Miramaksimus/HOTAS-Joystick-Soleil/images/3.png

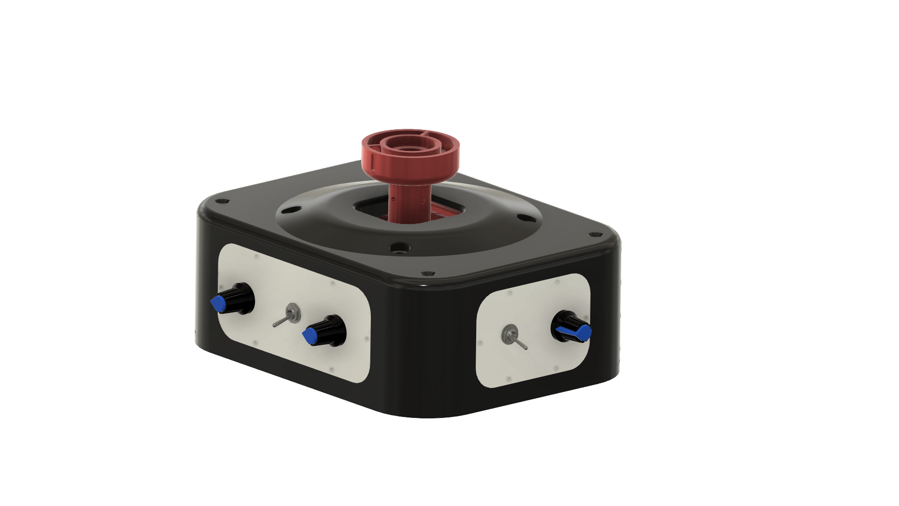
images/3.png
