Miramaksimus/HOTAS-Joystick-Soleil/export/housing/rectangular/stl/box_frame.stl

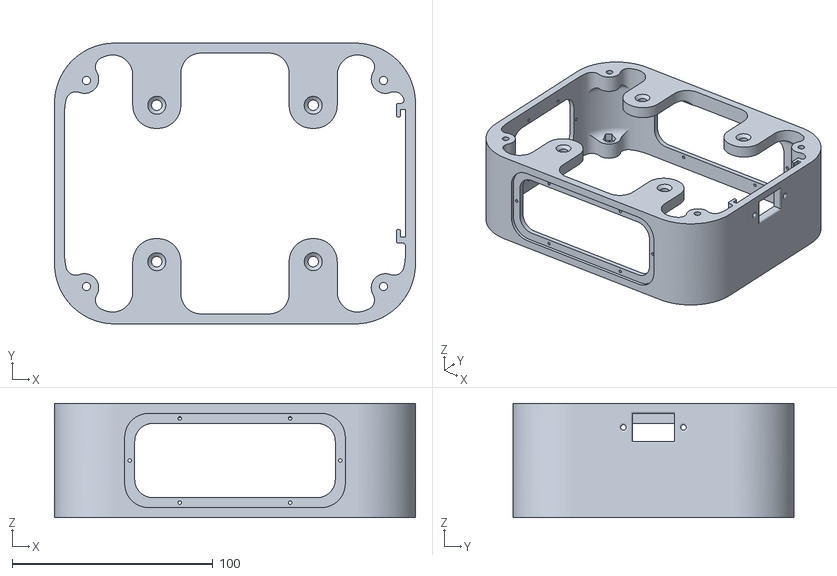
[picture p22: CAD file, 2023-05-21]
export/housing/rectangular/stl/box_frame.stl
180.0 x 140.0 x 57.0
