Miramaksimus/HOTAS-Joystick-Soleil/export/stick/common_parts/stl/dms_hat.stl

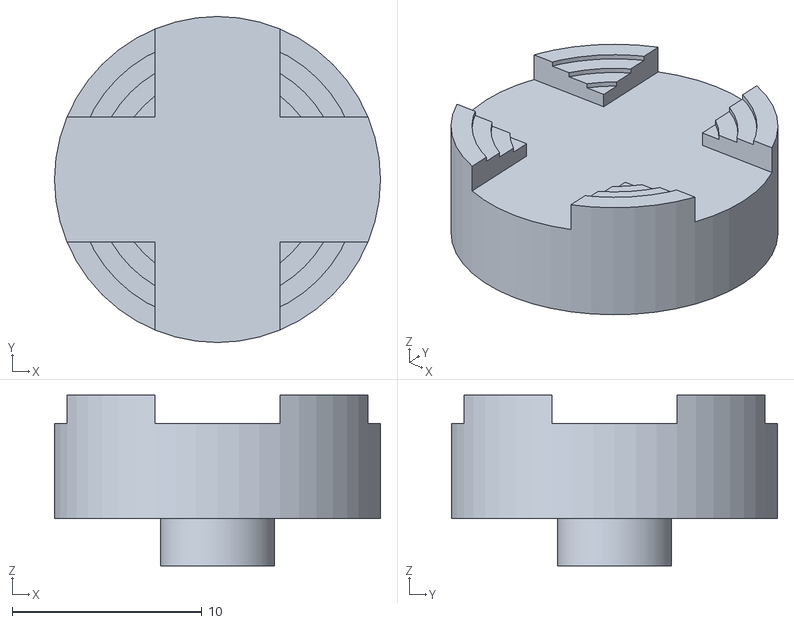
[picture p23: CAD file, 2024-08-11]
export/stick/common_parts/stl/dms_hat.stl
17.2 x 17.2 x 9.00
