Miramaksimus/HOTAS-Joystick-Soleil/export/twist/stl/gimbal_lever_arm.stl

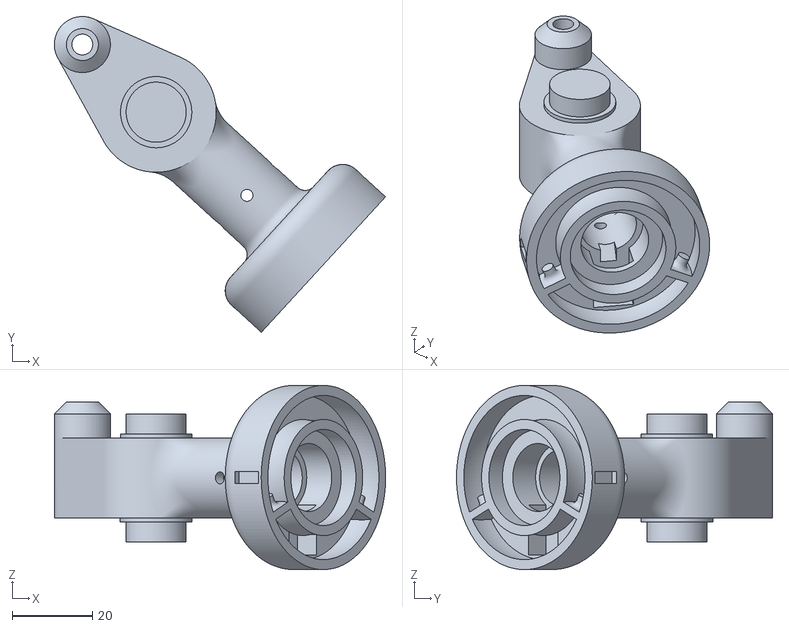
[picture p24: CAD file, 2023-04-30]
export/twist/stl/gimbal_lever_arm.stl
82.7 x 78.9 x 46.0
