Miramaksimus/HOTAS-Joystick-Soleil/export/gimbal/stl/gimbal_core_bearing_carrier_alt.stl

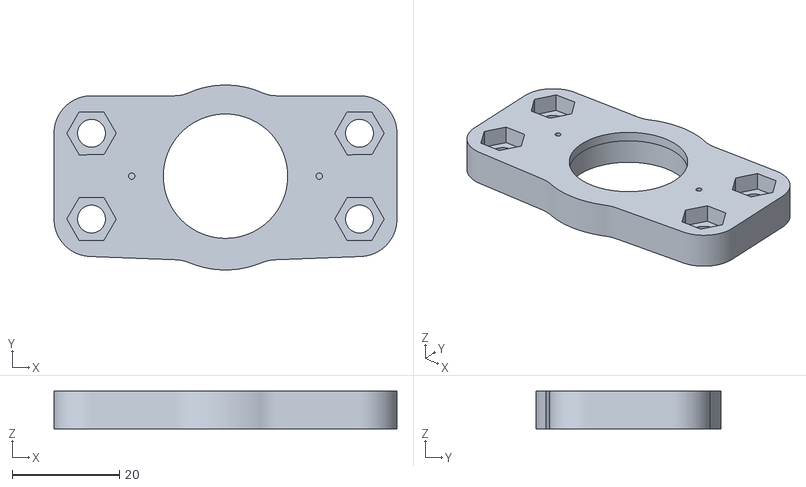
[picture p25: CAD file, 2023-04-30]
export/gimbal/stl/gimbal_core_bearing_carrier_alt.stl
64.0 x 34.5 x 7.00
