Miramaksimus/HOTAS-Joystick-Soleil/export/housing/cylindrical/stl/housing_body.stl

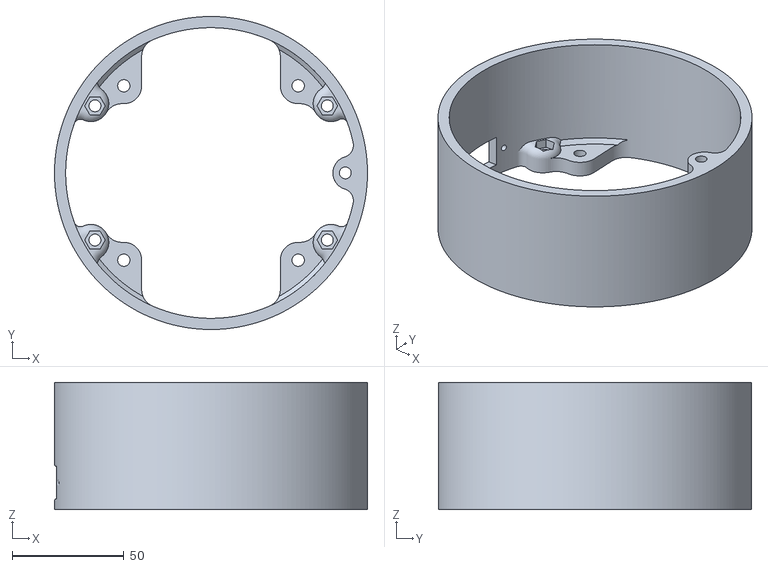
[picture p26: CAD file, 2023-04-30]
export/housing/cylindrical/stl/housing_body.stl
140.0 x 140.0 x 57.0
