Miramaksimus/HOTAS-Joystick-Soleil/export/housing/rectangular/stl/front_cover.stl

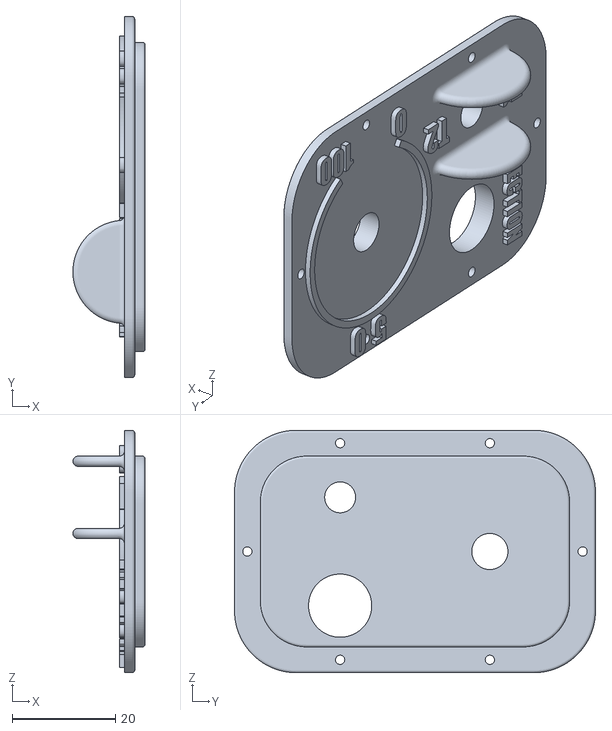
[picture p27: CAD file, 2023-05-21]
export/housing/rectangular/stl/front_cover.stl
14.0 x 70.0 x 47.0
