Miramaksimus/HOTAS-Joystick-Soleil/export/stick/common_parts/stl/tact_switch_cover.stl

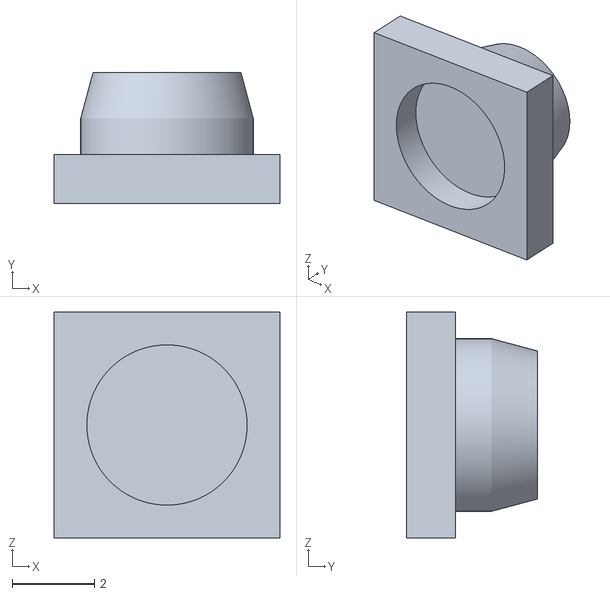
[picture p28: CAD file, 2024-08-11]
export/stick/common_parts/stl/tact_switch_cover.stl
5.50 x 3.20 x 5.50
