Miramaksimus/HOTAS-Joystick-Soleil/export/twist/stl/twist_adapder_top.stl

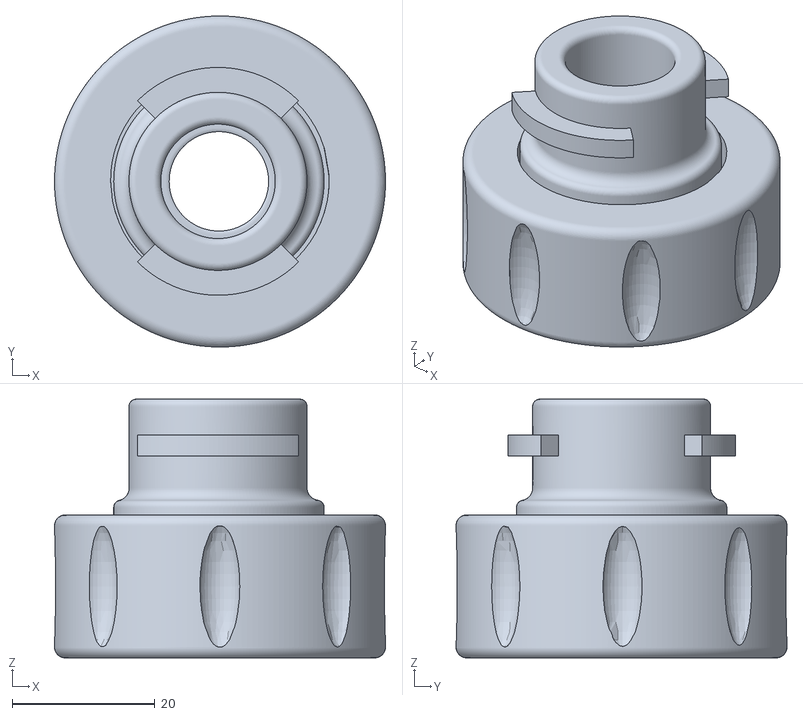
[picture p29: CAD file, 2023-04-30]
export/twist/stl/twist_adapder_top.stl
46.3 x 46.3 x 36.2
