Miramaksimus/HOTAS-Joystick-Soleil/export/gimbal/stl/gimbal_core_non_pot_side.stl

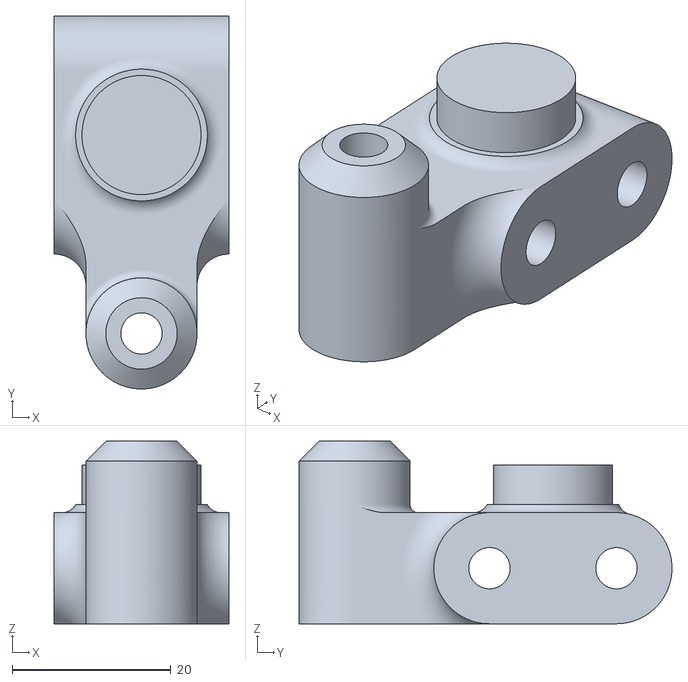
[picture p30: CAD file, 2023-04-30]
export/gimbal/stl/gimbal_core_non_pot_side.stl
22.0 x 47.0 x 23.0
