Miramaksimus/HOTAS-Joystick-Soleil/export/housing/cylindrical/stl/housing_bluepill-1.6mm.stl

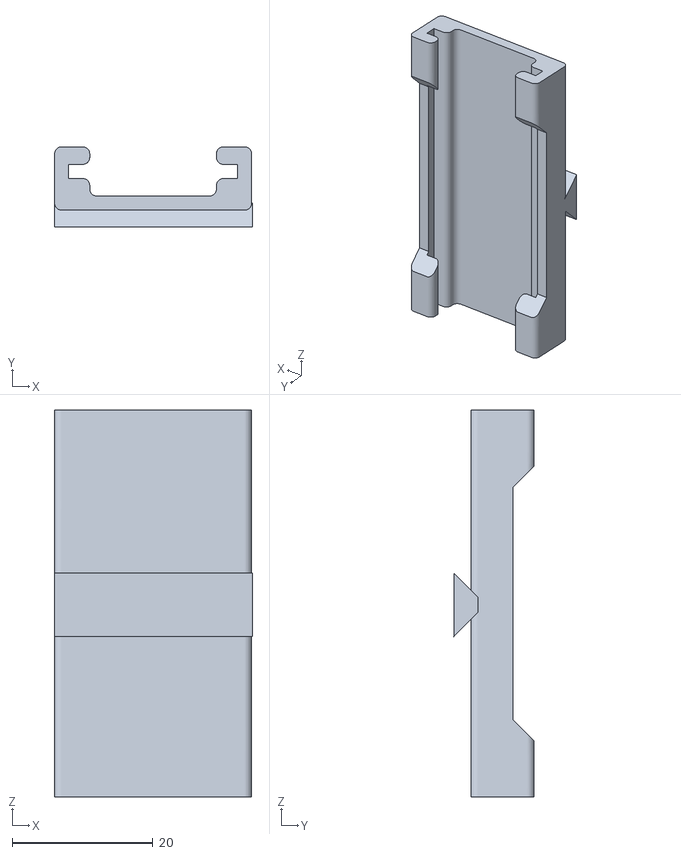
[picture p31: CAD file, 2023-04-30]
export/housing/cylindrical/stl/housing_bluepill-1.6mm.stl
28.2 x 11.4 x 55.0
