Miramaksimus/HOTAS-Joystick-Soleil/export/housing/rectangular/stl/box_bottom.stl

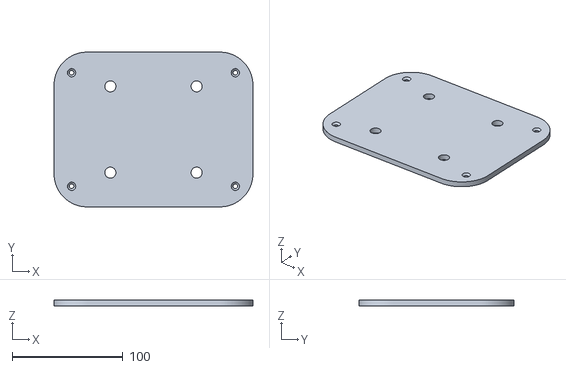
[picture p32: CAD file, 2023-05-21]
export/housing/rectangular/stl/box_bottom.stl
180.0 x 140.0 x 5.00
