Miramaksimus/HOTAS-Joystick-Soleil/export/stick/common_parts/stl/paddle.stl

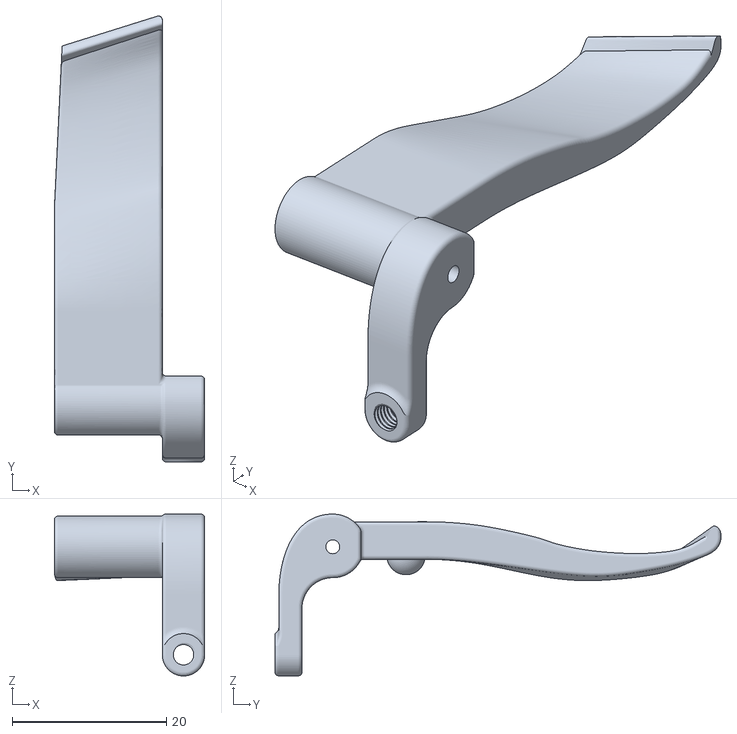
[picture p33: CAD file, 2024-08-11]
export/stick/common_parts/stl/paddle.stl
19.5 x 57.9 x 21.0
