Miramaksimus/HOTAS-Joystick-Soleil/export/twist/stl/twist_rudder_controls_top.stl

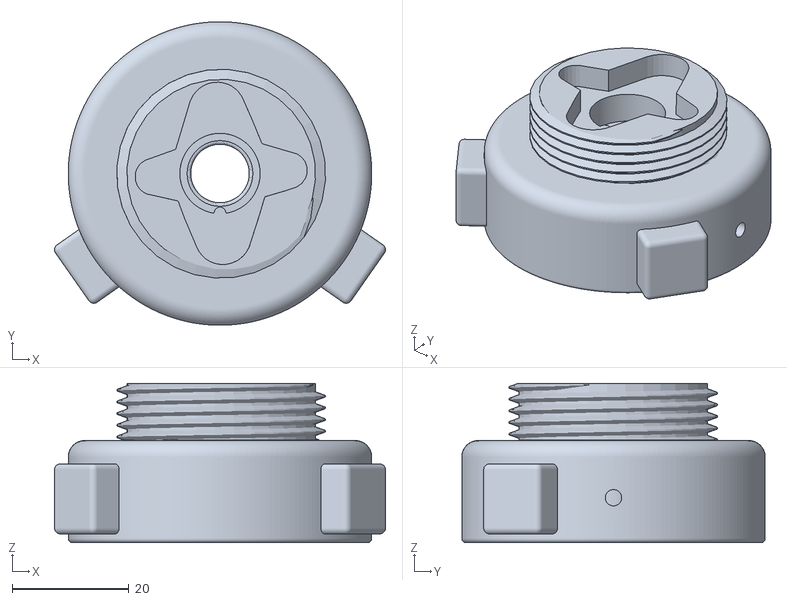
[picture p34: CAD file, 2023-04-30]
export/twist/stl/twist_rudder_controls_top.stl
56.7 x 52.0 x 27.3
