Miramaksimus/HOTAS-Joystick-Soleil/export/gimbal/stl/gimbal_cam.stl

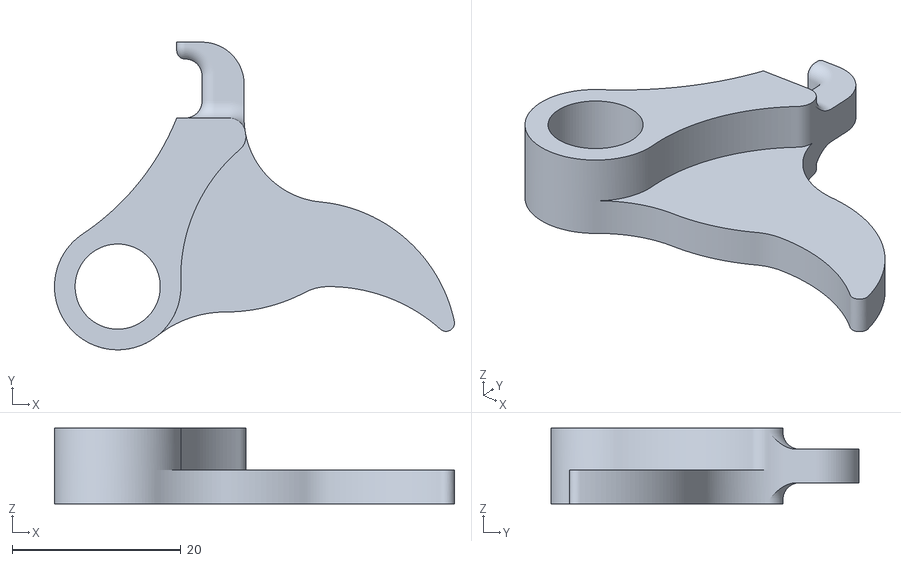
[picture p35: CAD file, 2023-04-30]
export/gimbal/stl/gimbal_cam.stl
47.5 x 36.5 x 9.00
