Miramaksimus/HOTAS-Joystick-Soleil/export/housing/rectangular/stl/right_cover.stl

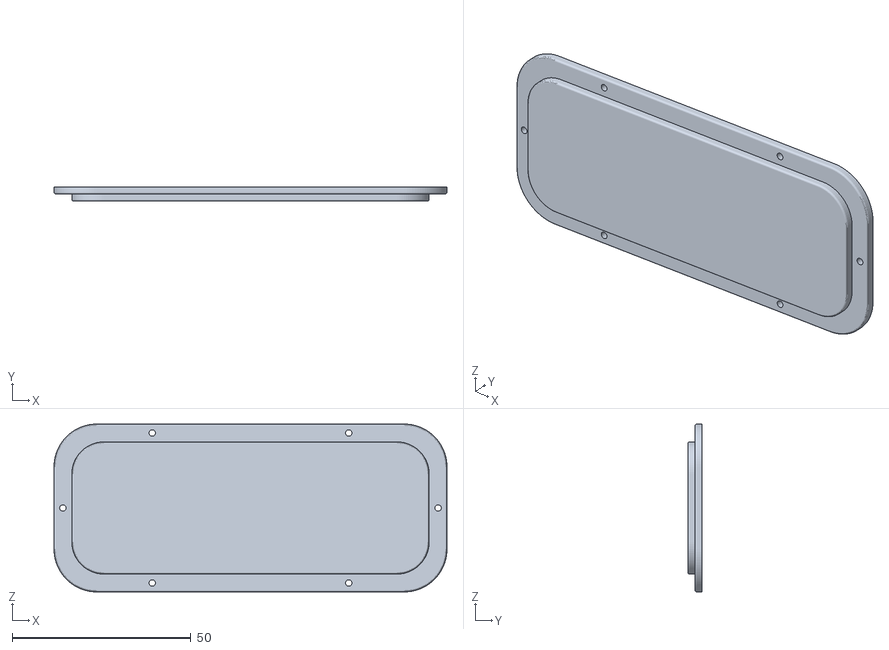
[picture p36: CAD file, 2023-05-21]
export/housing/rectangular/stl/right_cover.stl
110.0 x 4.00 x 47.0
