Miramaksimus/HOTAS-Joystick-Soleil/export/stick/common_parts/stl/trim_hat.stl

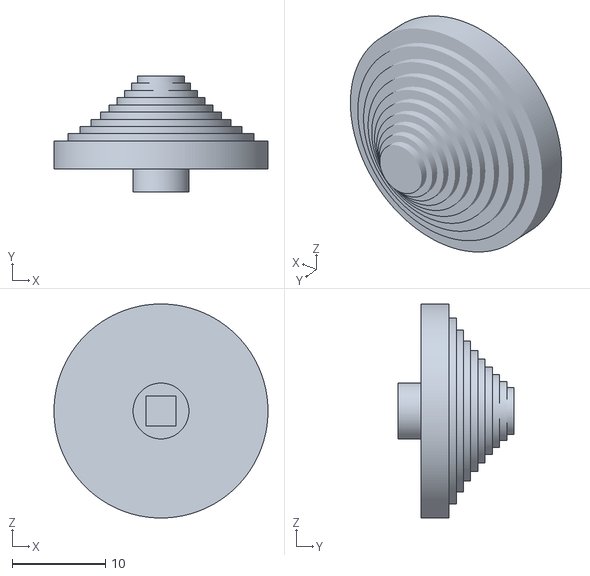
[picture p37: CAD file, 2024-08-11]
export/stick/common_parts/stl/trim_hat.stl
23.0 x 12.5 x 23.0
