Miramaksimus/HOTAS-Joystick-Soleil/export/housing/rectangular/stl/left_cover.stl

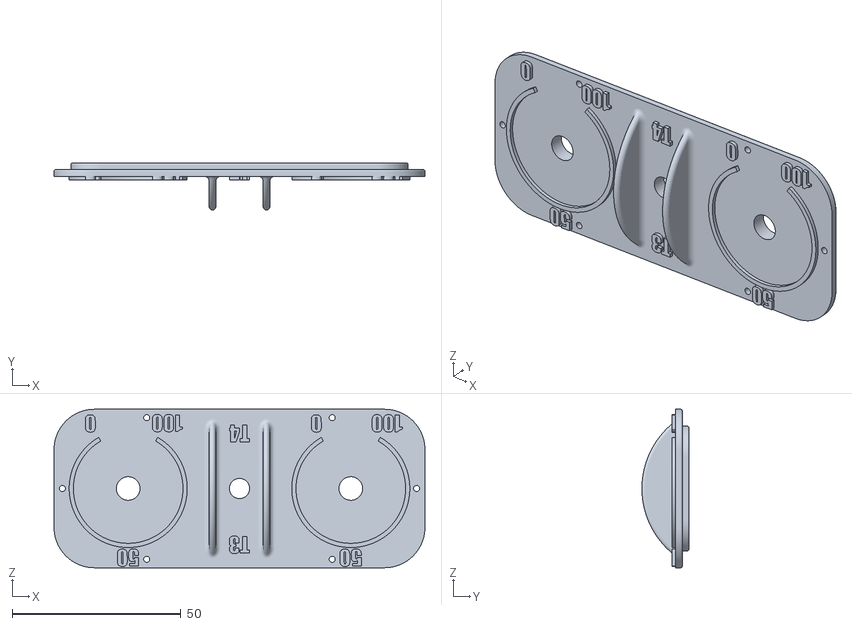
[picture p38: CAD file, 2023-05-21]
export/housing/rectangular/stl/left_cover.stl
110.0 x 14.0 x 47.0
