Miramaksimus/HOTAS-Joystick-Soleil/export/stick/common_parts/stl/tms_hat.stl

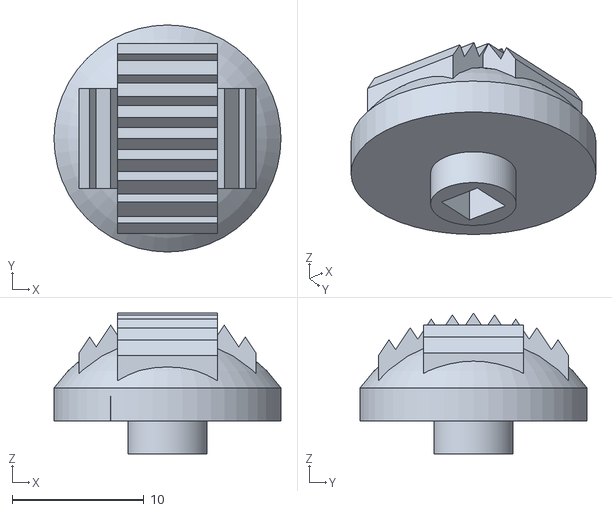
[picture p39: CAD file, 2024-08-11]
export/stick/common_parts/stl/tms_hat.stl
17.2 x 17.2 x 10.7
