Miramaksimus/HOTAS-Joystick-Soleil/export/housing/rectangular/stl/potentiometr_knob.stl

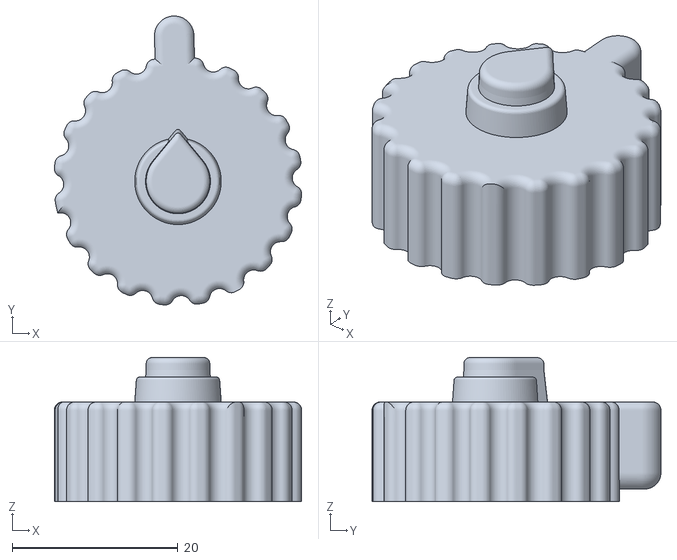
[picture p40: CAD file, 2023-05-21]
export/housing/rectangular/stl/potentiometr_knob.stl
29.8 x 34.8 x 17.4
