Miramaksimus/HOTAS-Joystick-Soleil/export/stick/common_parts/stl/button_side.stl

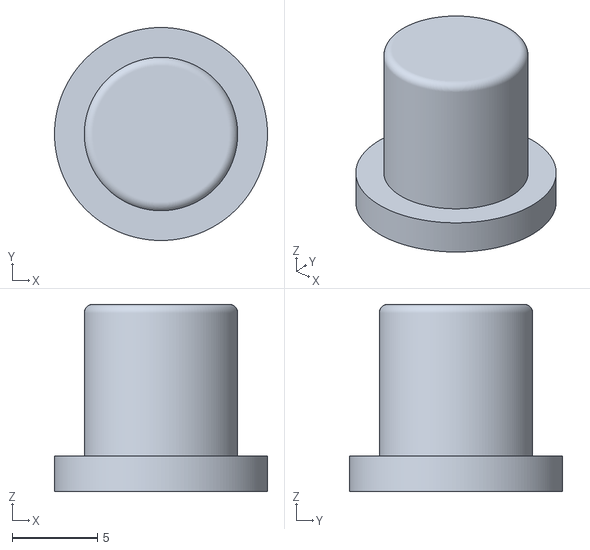
[picture p41: CAD file, 2024-08-11]
export/stick/common_parts/stl/button_side.stl
12.5 x 12.5 x 11.0
