Miramaksimus/HOTAS-Joystick-Soleil/export/housing/rectangular/stl/box_cover.stl

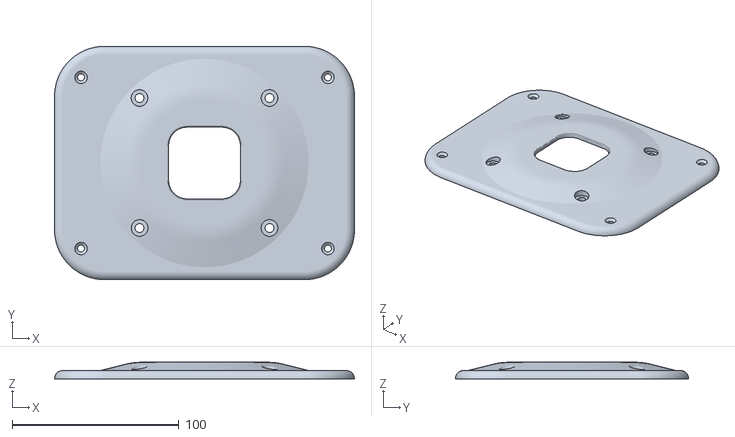
[picture p42: CAD file, 2023-05-21]
export/housing/rectangular/stl/box_cover.stl
180.0 x 140.0 x 10.0
