Miramaksimus/HOTAS-Joystick-Soleil/export/stick/common_parts/stl/trigger.stl

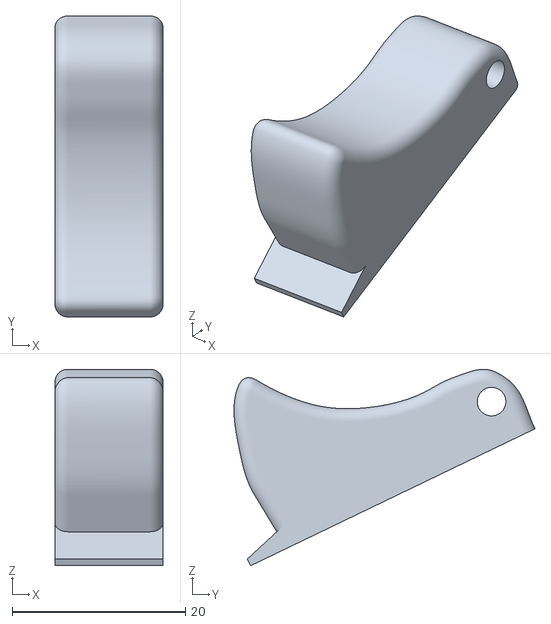
[picture p43: CAD file, 2024-08-11]
export/stick/common_parts/stl/trigger.stl
12.5 x 34.8 x 22.7
