Miramaksimus/HOTAS-Joystick-Soleil/export/housing/rectangular/stl/button_red_cap.stl

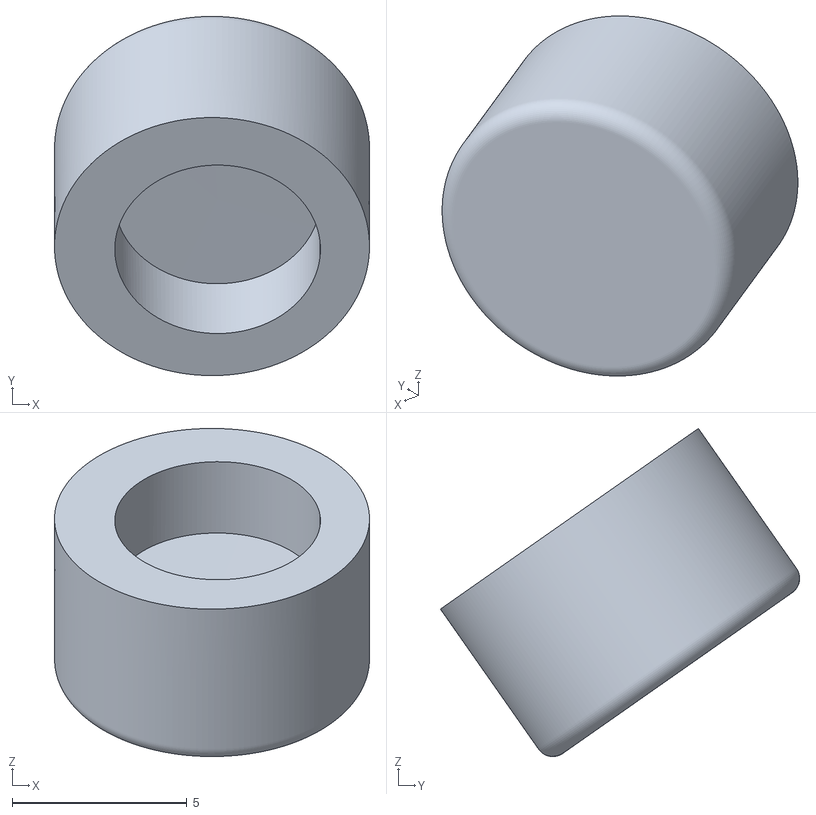
[picture p44: CAD file, 2023-05-21]
export/housing/rectangular/stl/button_red_cap.stl
9.00 x 10.3 x 9.37
