Miramaksimus/HOTAS-Joystick-Soleil/export/stick/common_parts/stl/button_ctrl.stl

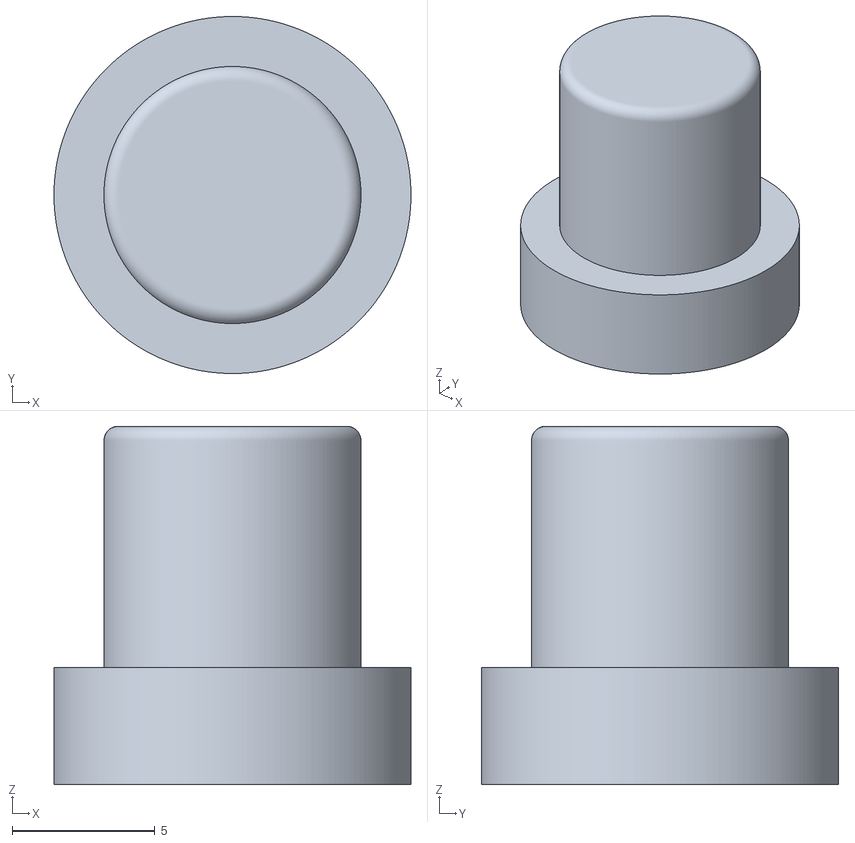
[picture p45: CAD file, 2024-08-11]
export/stick/common_parts/stl/button_ctrl.stl
12.5 x 12.5 x 12.5
