Miramaksimus/HOTAS-Joystick-Soleil/export/housing/rectangular/stl/soleil.stl

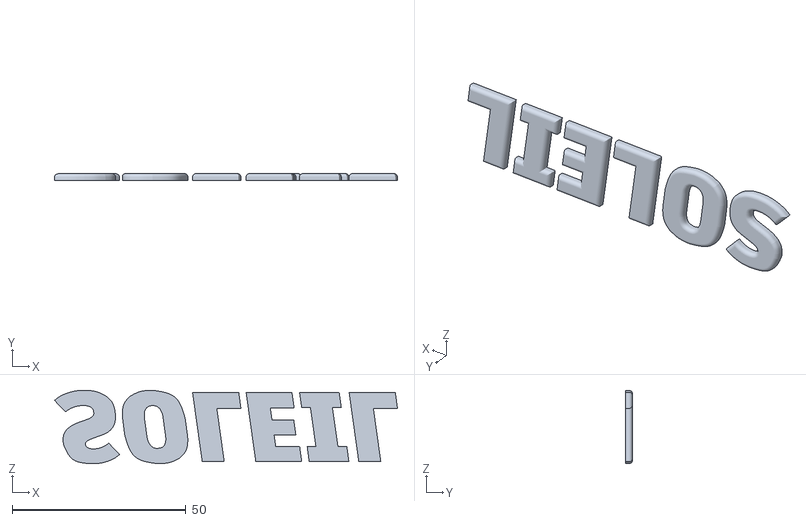
[picture p46: CAD file, 2023-05-21]
export/housing/rectangular/stl/soleil.stl
98.8 x 2.00 x 21.1
