Miramaksimus/HOTAS-Joystick-Soleil/export/stick/common_parts/stl/hat-switch-base.stl

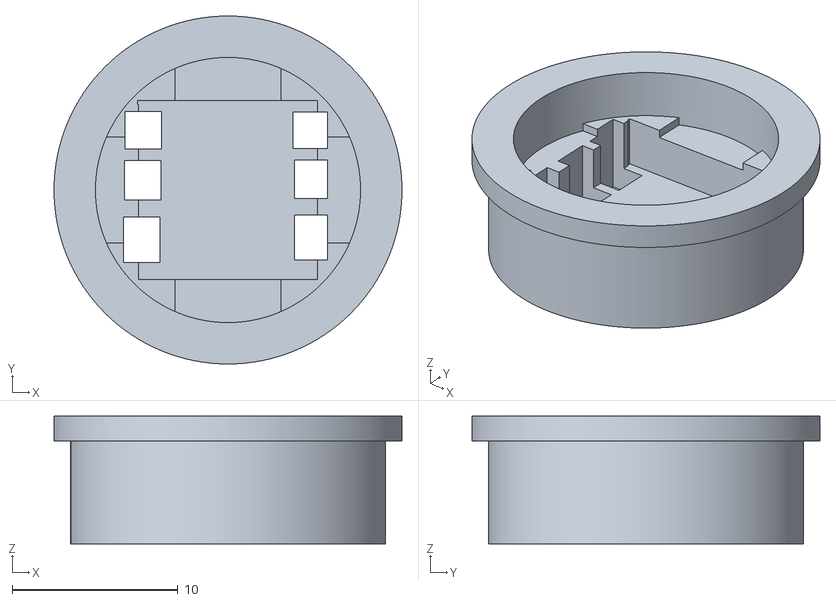
[picture p47: CAD file, 2023-06-24]
export/stick/common_parts/stl/hat-switch-base.stl
21.0 x 21.0 x 7.70
