Miramaksimus/HOTAS-Joystick-Soleil/export/stick/common_parts/stl/Face_alter.stl

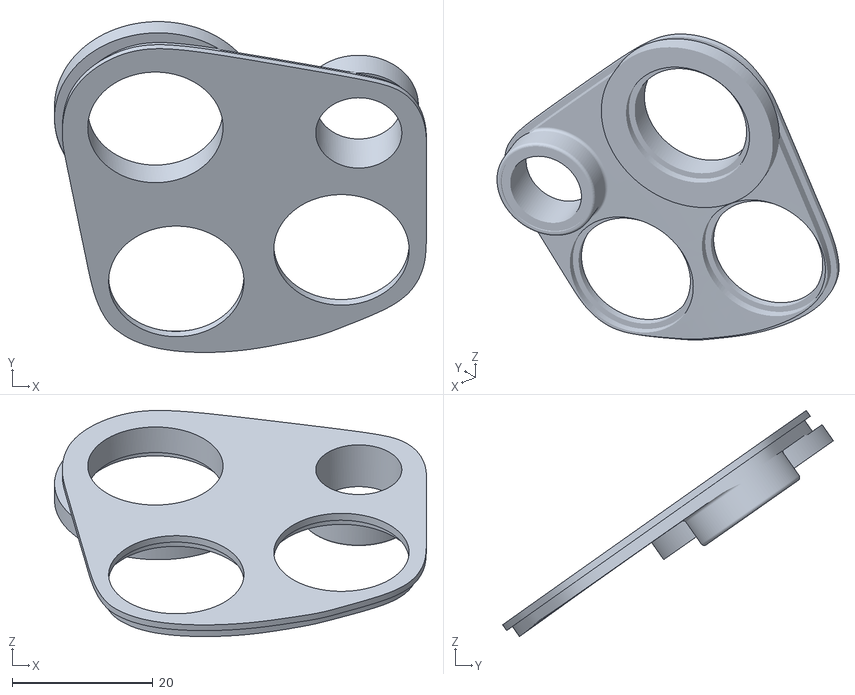
[picture p48: CAD file, 2023-06-24]
export/stick/common_parts/stl/Face_alter.stl
52.9 x 47.1 x 32.2
