Miramaksimus/HOTAS-Joystick-Soleil/export/stick/common_parts/stl/Top.stl

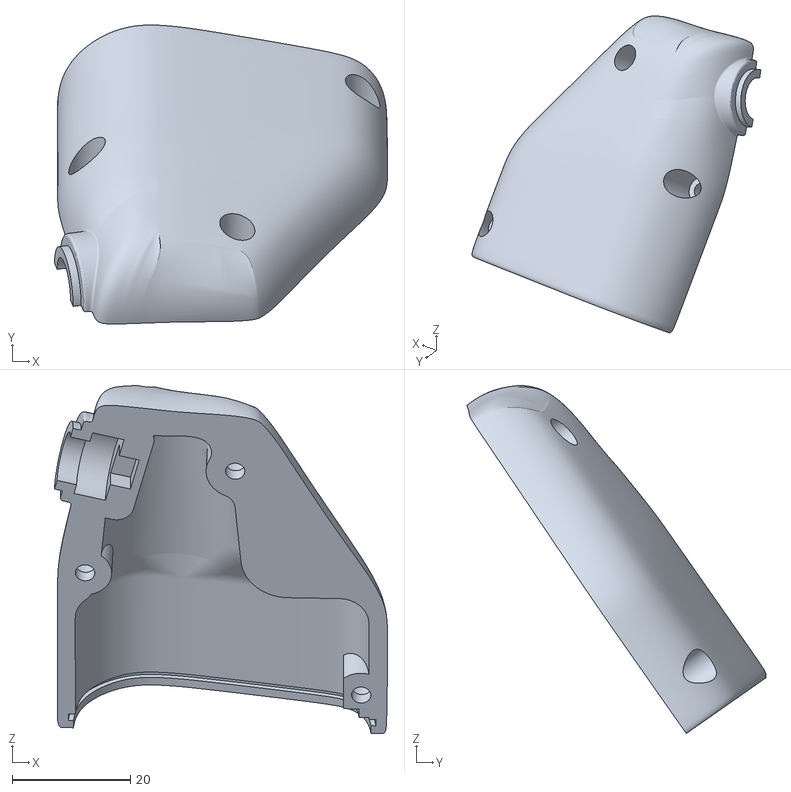
[picture p49: CAD file, 2023-06-24]
export/stick/common_parts/stl/Top.stl
56.4 x 50.6 x 58.9
