Miramaksimus/HOTAS-Joystick-Soleil/export/stick/common_parts/stl/Face.stl

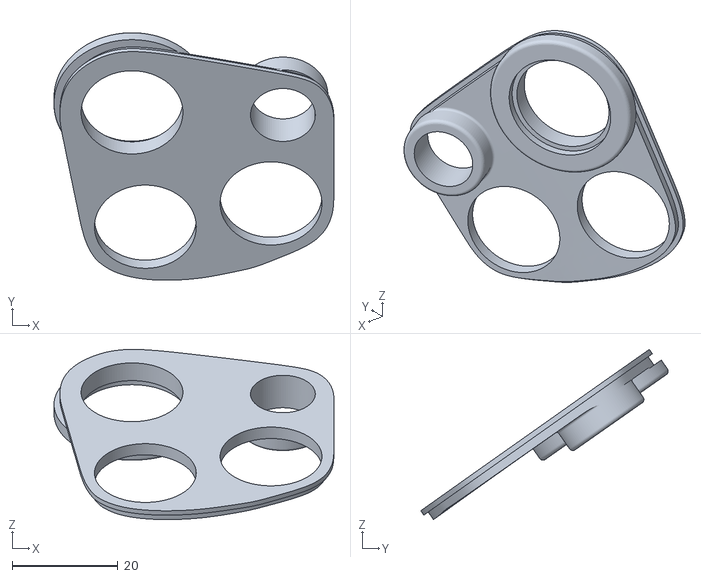
[picture p50: CAD file, 2023-06-24]
export/stick/common_parts/stl/Face.stl
52.9 x 46.8 x 32.2
