Miramaksimus/HOTAS-Joystick-Soleil/export/stick/common_parts/stl/hat-switch-base-cap.stl

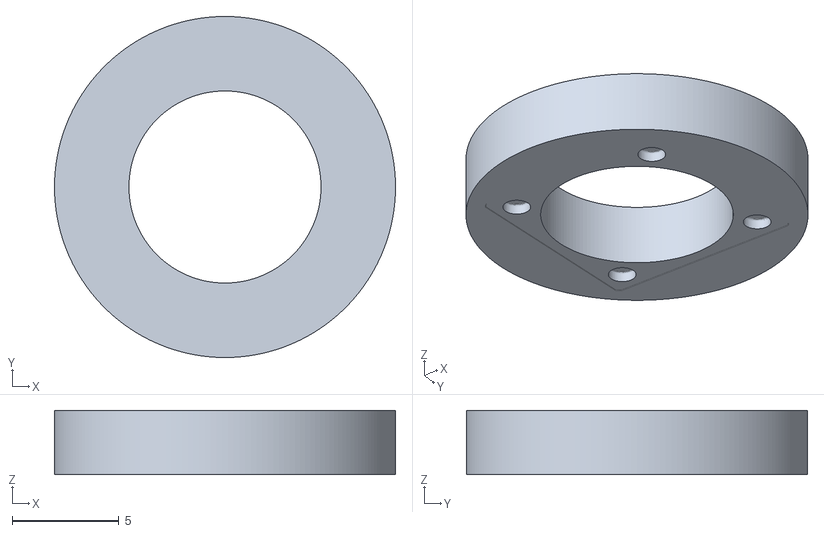
[picture p51: CAD file, 2023-06-24]
export/stick/common_parts/stl/hat-switch-base-cap.stl
16.0 x 16.0 x 3.00
