Miramaksimus/HOTAS-Joystick-Soleil/export/stick/common_parts/stl/button_cover.stl

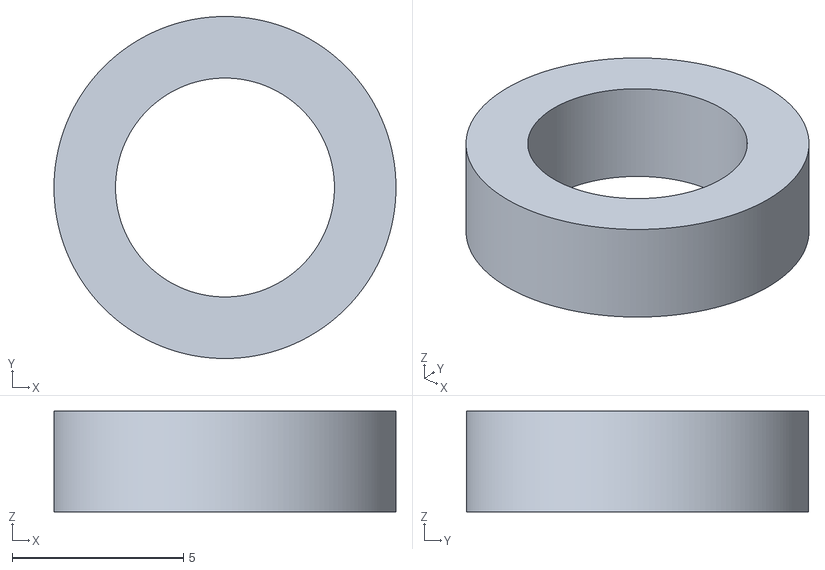
[picture p52: CAD file, 2023-05-21]
export/stick/common_parts/stl/button_cover.stl
10.00 x 10.00 x 2.95
