Miramaksimus/HOTAS-Joystick-Soleil/export/stick/common_parts/stl/button_base.stl

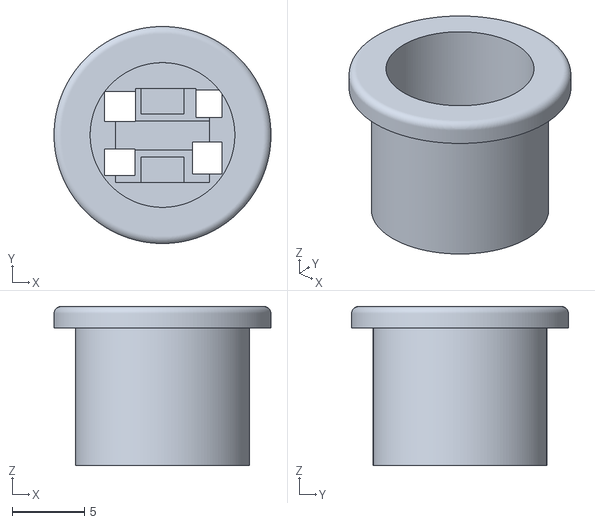
[picture p53: CAD file, 2023-05-21]
export/stick/common_parts/stl/button_base.stl
15.0 x 15.0 x 11.0
